cmock/stromkosten-display/src/awattar_testdata.h

char testdata[] = "{\
  \"object\": \"list\",\
  \"data\": [\
    {\
      \"start_timestamp\": 1685512800000,\
      \"end_timestamp\": 1685516400000,\
      \"marketprice\": 100.01,\
      \"unit\": \"Eur/MWh\"\
    },\
    {\
      \"start_timestamp\": 1685516400000,\
      \"end_timestamp\": 1685520000000,\
      \"marketprice\": 86.41,\
      \"unit\": \"Eur/MWh\"\
    },\
    {\
      \"start_timestamp\": 1685520000000,\
      \"end_timestamp\": 1685523600000,\
      \"marketprice\": 66.92,\
      \"unit\": \"Eur/MWh\"\
    },\
    {\
      \"start_timestamp\": 1685523600000,\
      \"end_timestamp\": 1685527200000,\
      \"marketprice\": 46.12,\
      \"unit\": \"Eur/MWh\"\
    },\
    {\
      \"start_timestamp\": 1685527200000,\
      \"end_timestamp\": 1685530800000,\
      \"marketprice\": 50.04,\
      \"unit\": \"Eur/MWh\"\
    },\
    {\
      \"start_timestamp\": 1685530800000,\
      \"end_timestamp\": 1685534400000,\
      \"marketprice\": 46.83,\
      \"unit\": \"Eur/MWh\"\
    },\
    {\
      \"start_timestamp\": 1685534400000,\
      \"end_timestamp\": 1685538000000,\
      \"marketprice\": 47.47,\
      \"unit\": \"Eur/MWh\"\
    },\
    {\
      \"start_timestamp\": 1685538000000,\
      \"end_timestamp\": 1685541600000,\
      \"marketprice\": 34.16,\
      \"unit\": \"Eur/MWh\"\
    },\
    {\
      \"start_timestamp\": 1685541600000,\
      \"end_timestamp\": 1685545200000,\
      \"marketprice\": 58.04,\
      \"unit\": \"Eur/MWh\"\
    },\
    {\
      \"start_timestamp\": 1685545200000,\
      \"end_timestamp\": 1685548800000,\
      \"marketprice\": 63.66,\
      \"unit\": \"Eur/MWh\"\
    },\
    {\
      \"start_timestamp\": 1685548800000,\
      \"end_timestamp\": 1685552400000,\
      \"marketprice\": 94,\
      \"unit\": \"Eur/MWh\"\
    },\
    {\
      \"start_timestamp\": 1685552400000,\
      \"end_timestamp\": 1685556000000,\
      \"marketprice\": 114.87,\
      \"unit\": \"Eur/MWh\"\
    },\
    {\
      \"start_timestamp\": 1685556000000,\
      \"end_timestamp\": 1685559600000,\
      \"marketprice\": 118.48,\
      \"unit\": \"Eur/MWh\"\
    },\
    {\
      \"start_timestamp\": 1685559600000,\
      \"end_timestamp\": 1685563200000,\
      \"marketprice\": 103.4,\
      \"unit\": \"Eur/MWh\"\
    },\
    {\
      \"start_timestamp\": 1685563200000,\
      \"end_timestamp\": 1685566800000,\
      \"marketprice\": 93.99,\
      \"unit\": \"Eur/MWh\"\
    },\
    {\
      \"start_timestamp\": 1685566800000,\
      \"end_timestamp\": 1685570400000,\
      \"marketprice\": 83.13,\
      \"unit\": \"Eur/MWh\"\
    }\
  ],\
  \"url\": \"/at/v1/marketdata\"\
}";
